Snektron/glycon/glyco/src/flash.c

#include "flash.h"
#include "pinout.h"
#include "bus.h"
#include "timing.h"

#include "common/glycon.h"

#include <stddef.h>

#define FLASH_SOFTWARE_ID_MFG_ADDR (0x0000)
#define FLASH_SOFTWARE_ID_DEV_ADDR (0x0001)

// Write a particular command to flash (both the address and
// data parts). Includes delay.
static void flash_cmd(gly_addr_t addr, uint8_t data) {
    bus_write(addr, data);
    bus_pulse_flash_write();
}

// Prepare the system for writing a flash command
static void flash_begin_cmd(void) {
    bus_set_mode(BUS_MODE_WRITE_MEM);
}

void flash_byte_program(gly_addr_t address, uint8_t data) {
    if (!glycon_is_flash_addr(address)) // Don't attempt to write to RAM.
        return;
    flash_begin_cmd();
    flash_cmd(0x5555, 0xAA);
    flash_cmd(0x2AAA, 0x55);
    flash_cmd(0x5555, 0xA0);
    flash_cmd(address, data);
    timing_flash_write_delay();
}

static void flash_enter_software_id_mode(void) {
    flash_begin_cmd();
    flash_cmd(0x5555, 0xAA);
    flash_cmd(0x2AAA, 0x55);
    flash_cmd(0x5555, 0x90);
}

static void flash_exit_software_id_mode(void) {
    flash_begin_cmd();
    flash_cmd(0x5555, 0xAA);
    flash_cmd(0x2AAA, 0x55);
    flash_cmd(0x5555, 0xF0);
}

void flash_get_software_id(uint8_t* mfg, uint8_t* dev) {
    flash_enter_software_id_mode();
    bus_set_mode(BUS_MODE_READ_MEM);
    *mfg = bus_read(FLASH_SOFTWARE_ID_MFG_ADDR);
    *dev = bus_read(FLASH_SOFTWARE_ID_DEV_ADDR);
    flash_exit_software_id_mode();
}

void flash_erase_sector(gly_addr_t sector_address) {
    if (!glycon_is_flash_addr(sector_address)) // Don't attempt to erase RAM.
        return;
    flash_begin_cmd();
    flash_cmd(0x5555, 0xAA);
    flash_cmd(0x2AAA, 0x55);
    flash_cmd(0x5555, 0x80);
    flash_cmd(0x5555, 0xAA);
    flash_cmd(0x2AAA, 0x55);
    flash_cmd(sector_address, 0x30);
    timing_flash_erase_sector_delay();
}

void flash_erase_chip() {
    flash_begin_cmd();
    flash_cmd(0x5555, 0xAA);
    flash_cmd(0x2AAA, 0x55);
    flash_cmd(0x5555, 0x80);
    flash_cmd(0x5555, 0xAA);
    flash_cmd(0x2AAA, 0x55);
    flash_cmd(0x5555, 0x10);
    timing_flash_erase_chip_delay();
}
